ShinoharaTa/keyboards/Shiro/pcb/Shiro/design/siro_mask.png

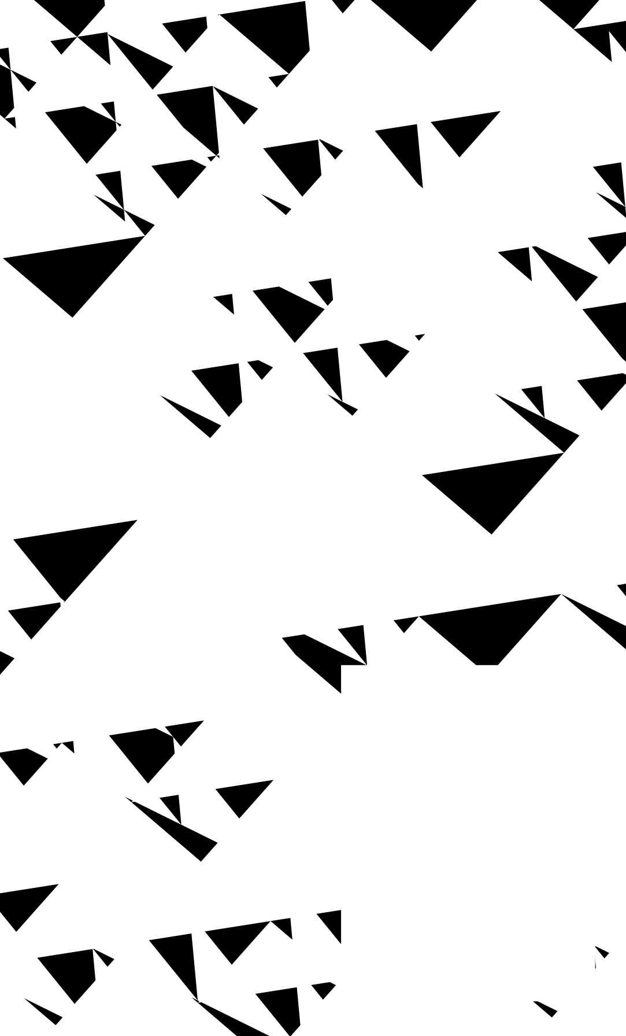
Shiro/pcb/Shiro/design/siro_mask.png
