ShinoharaTa/keyboards/Shiro/pcb/Shiro/design/siro_silk.png

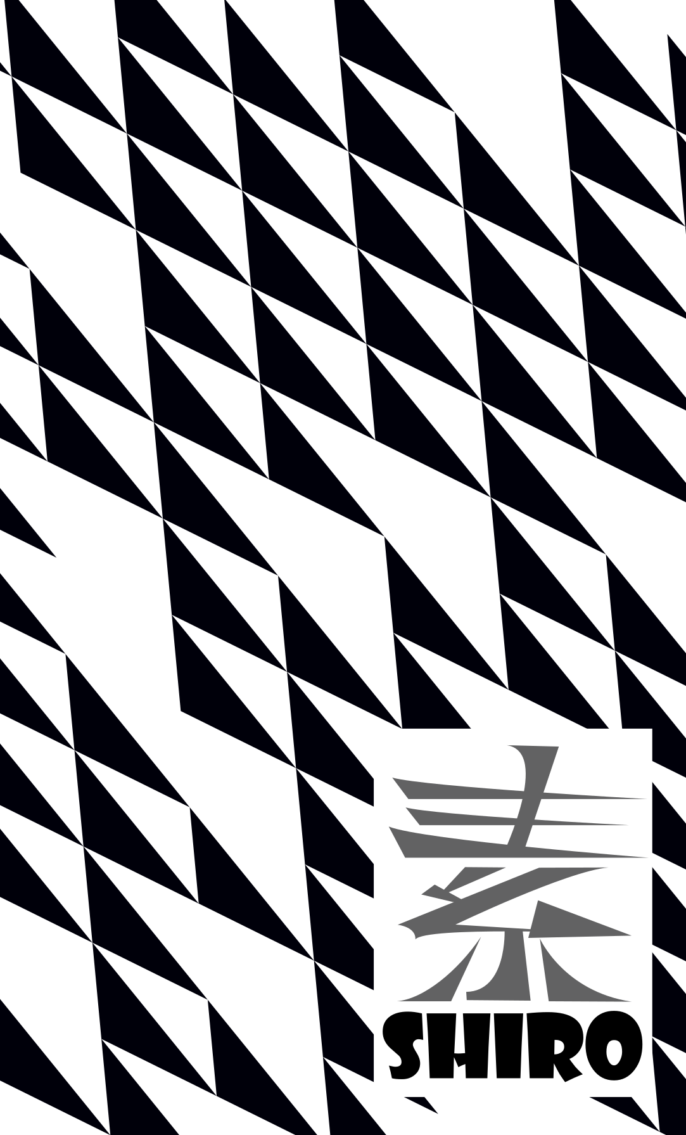
Shiro/pcb/Shiro/design/siro_silk.png
