ShinoharaTa/keyboards/RURA66/manual/images/IMG_0211.jpg

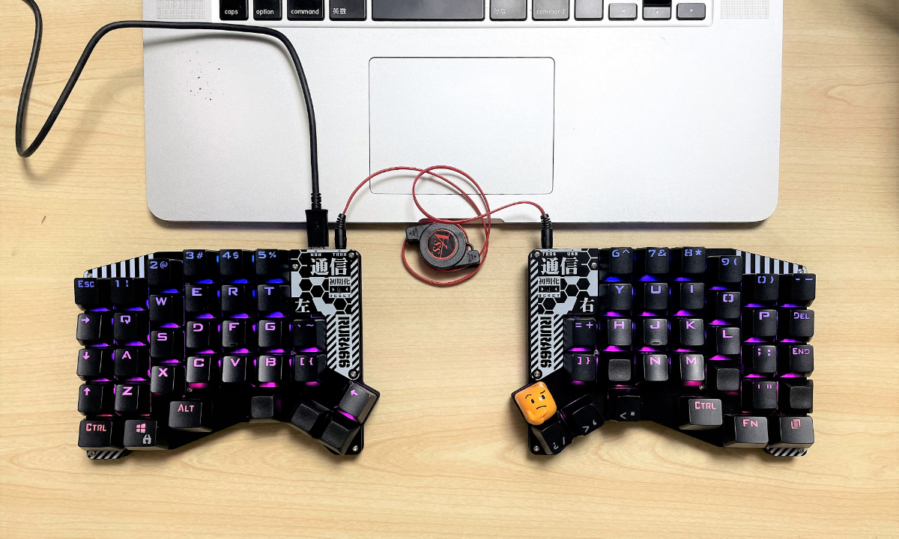
RURA66/manual/images/IMG_0211.jpg
