ShinoharaTa/keyboards/RURA66/manual/images/IMG_0212.jpg

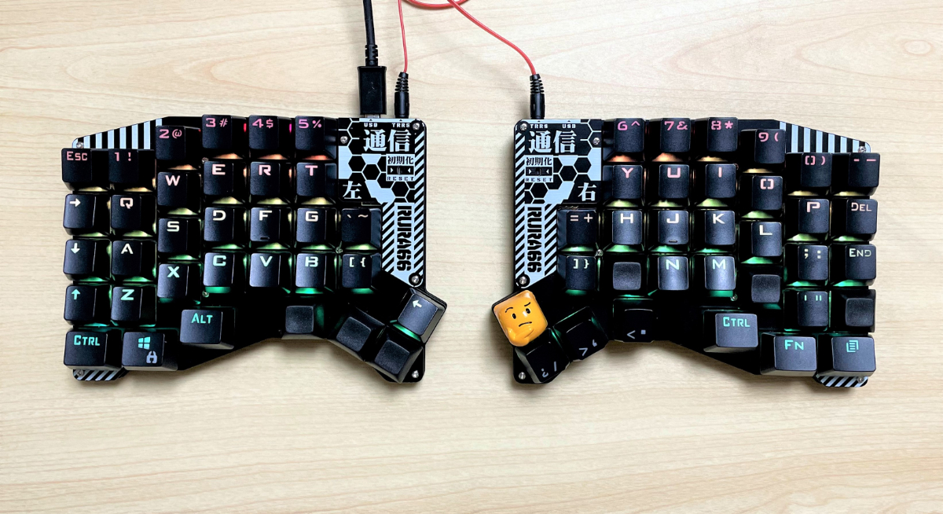
RURA66/manual/images/IMG_0212.jpg
