ShinoharaTa/keyboards/RURA66/manual/images/IMG_0217.jpg

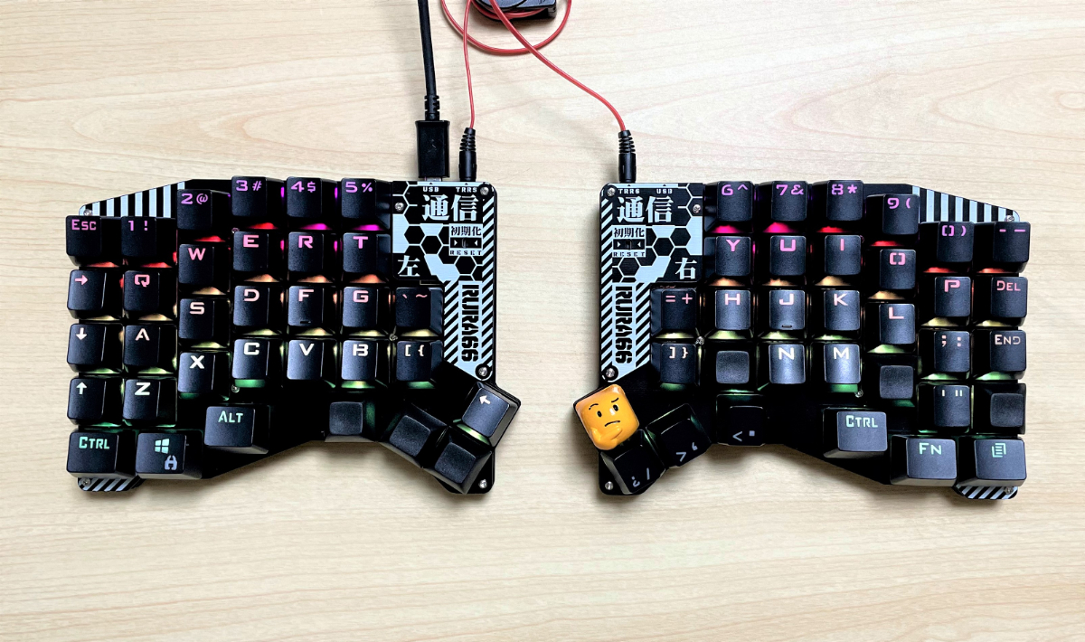
RURA66/manual/images/IMG_0217.jpg
