ShinoharaTa/keyboards/RURA66/manual/images/IMG_0218.jpg

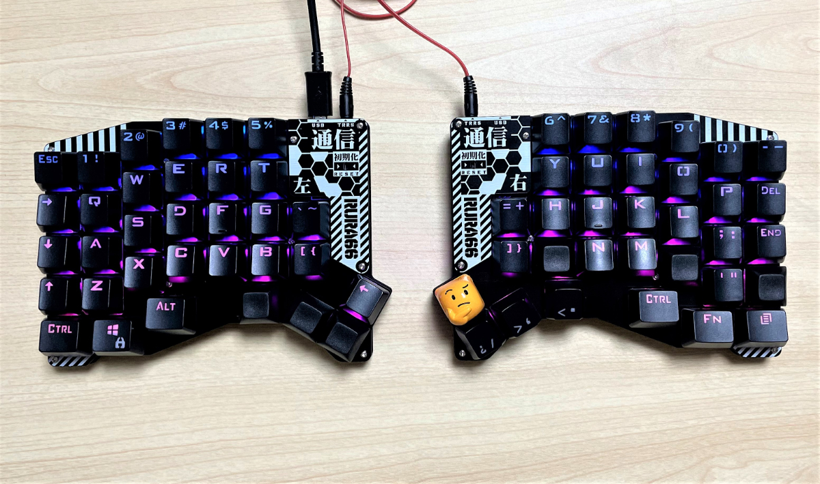
RURA66/manual/images/IMG_0218.jpg
