ShinoharaTa/keyboards/RURA66/manual/images/IMG_0220.jpg

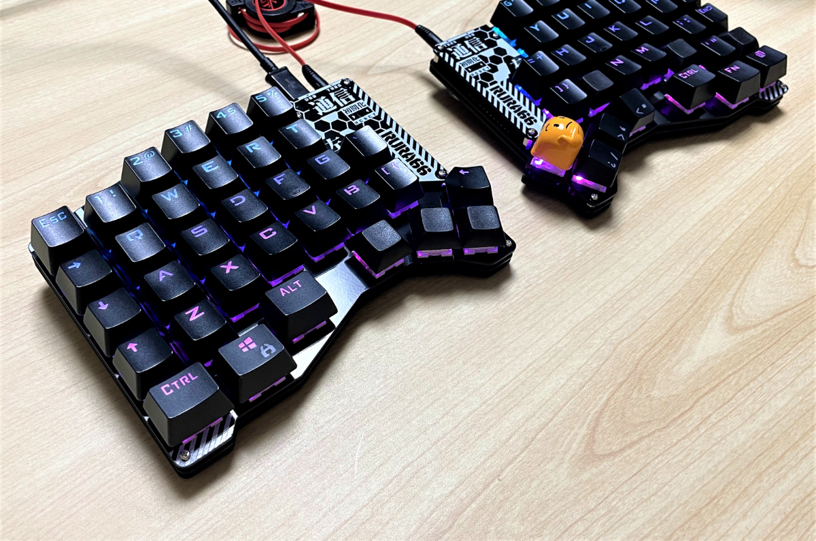
RURA66/manual/images/IMG_0220.jpg
