ShinoharaTa/keyboards/RURA66/manual/images/IMG_0231.jpg

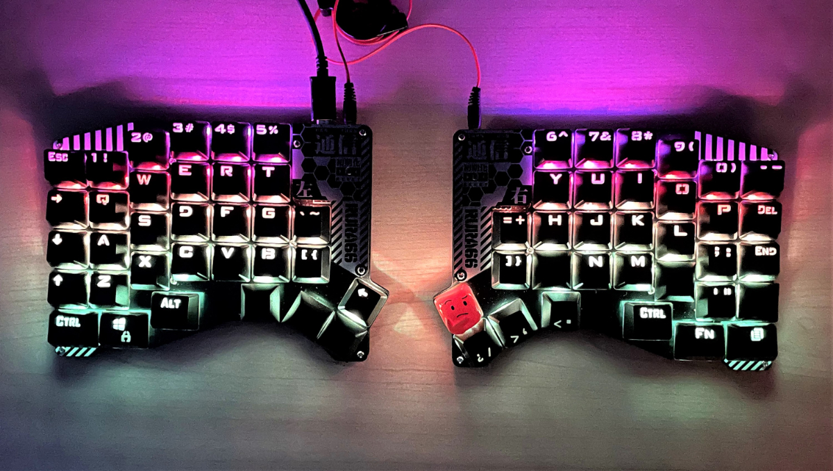
RURA66/manual/images/IMG_0231.jpg
