ShinoharaTa/keyboards/RURA66/manual/images/IMG_0232.jpg

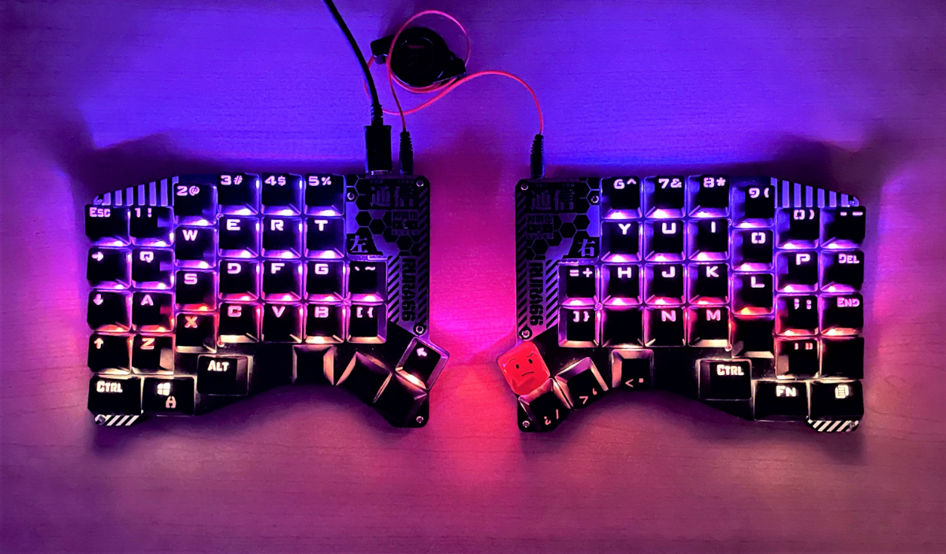
RURA66/manual/images/IMG_0232.jpg
