ShinoharaTa/keyboards/RURA66/manual/images/IMG_0242.jpg

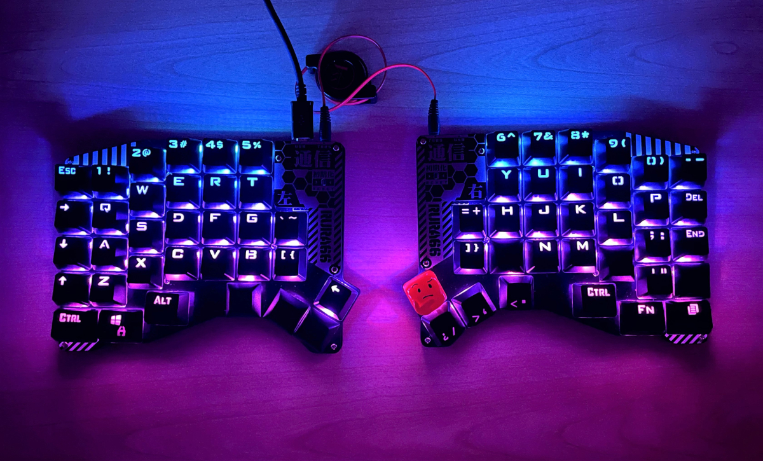
RURA66/manual/images/IMG_0242.jpg
