ShinoharaTa/keyboards/RURA66/manual/images/IMG_0276.jpg

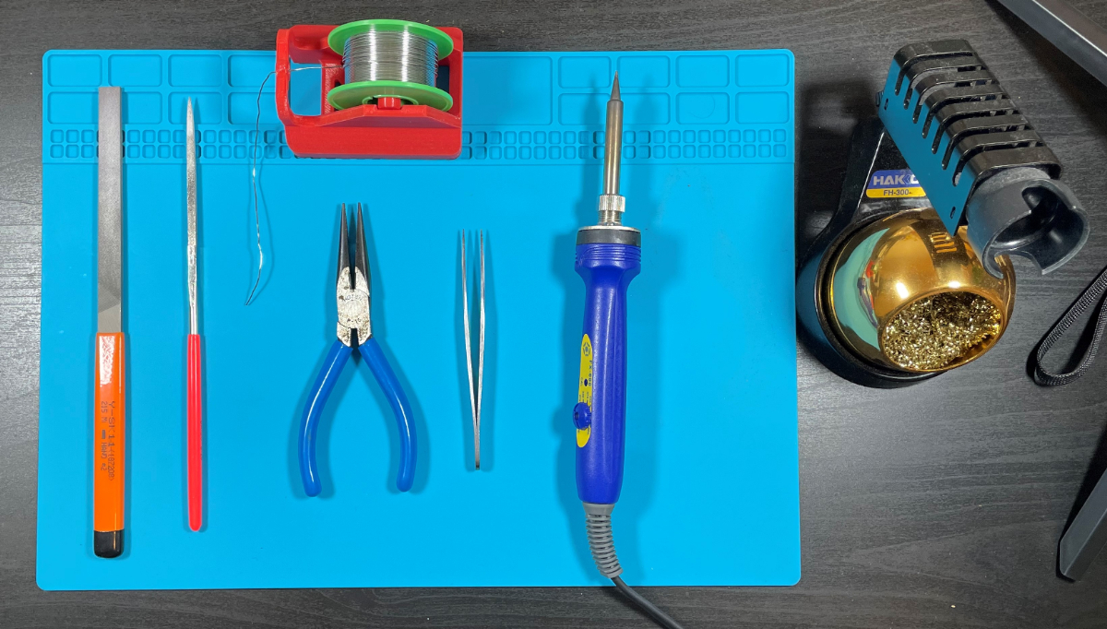
RURA66/manual/images/IMG_0276.jpg
