ShinoharaTa/keyboards/RURA66/manual/images/IMG_0283.jpg

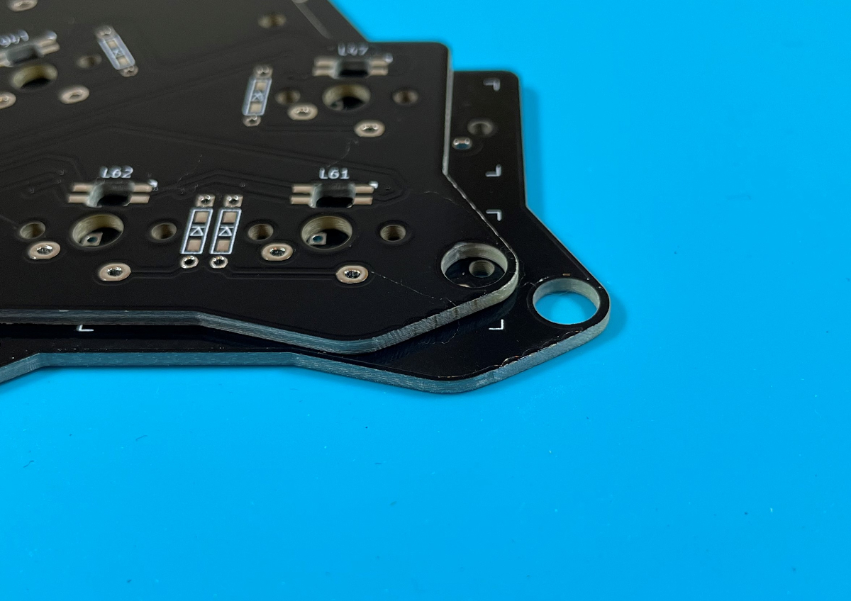
RURA66/manual/images/IMG_0283.jpg
