ShinoharaTa/keyboards/RURA66/manual/images/IMG_0285.jpg

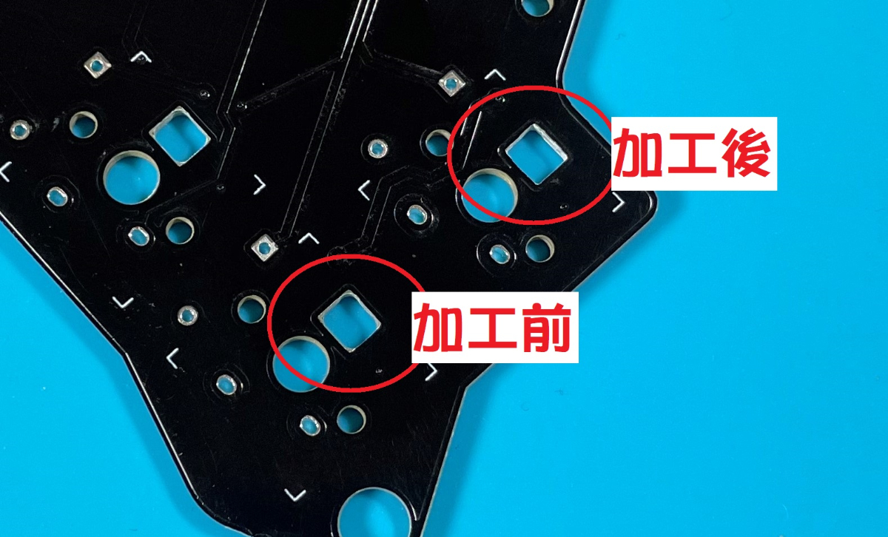
RURA66/manual/images/IMG_0285.jpg
