ShinoharaTa/keyboards/RURA66/manual/images/IMG_0292.jpg

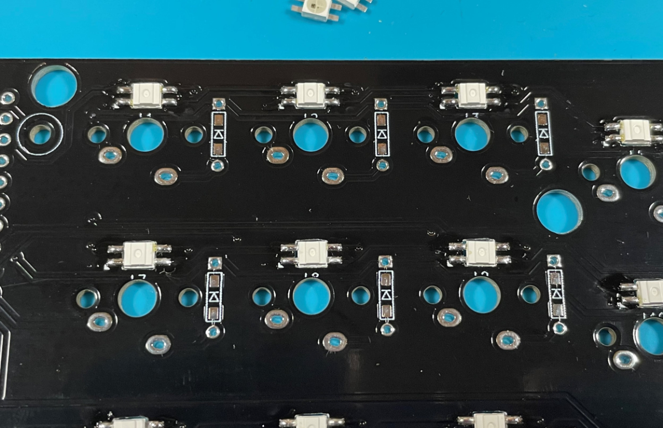
RURA66/manual/images/IMG_0292.jpg
