ShinoharaTa/keyboards/RURA66/manual/images/IMG_0301.jpg

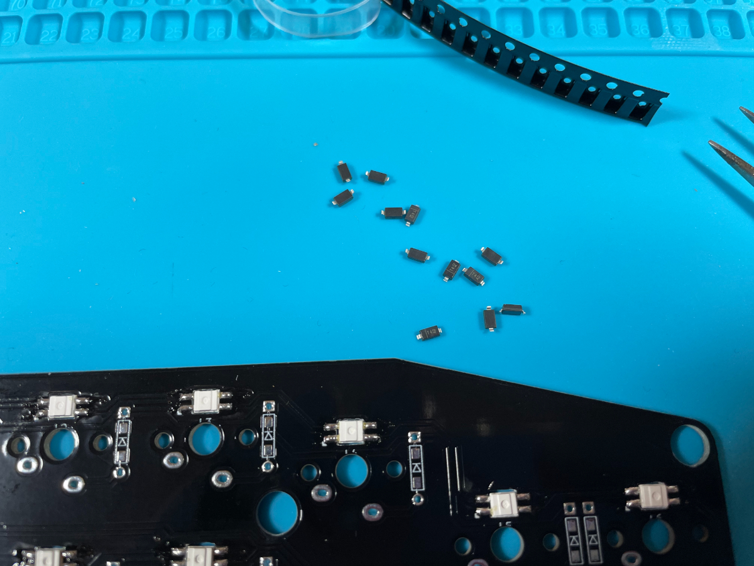
RURA66/manual/images/IMG_0301.jpg
