ShinoharaTa/keyboards/RURA66/manual/images/IMG_0330.jpg

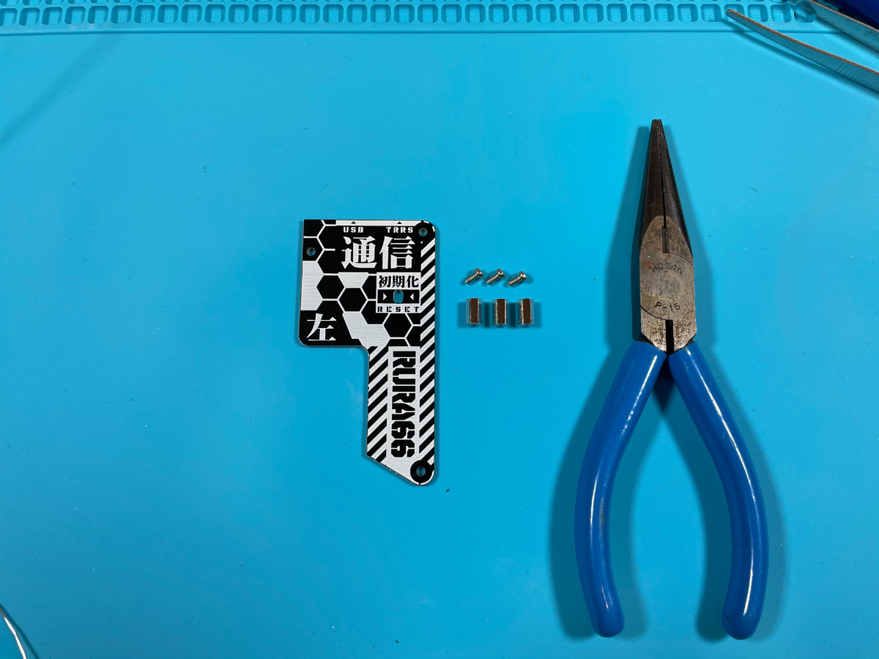
RURA66/manual/images/IMG_0330.jpg
