ShinoharaTa/keyboards/RURA66/manual/images/IMG_0333.jpg

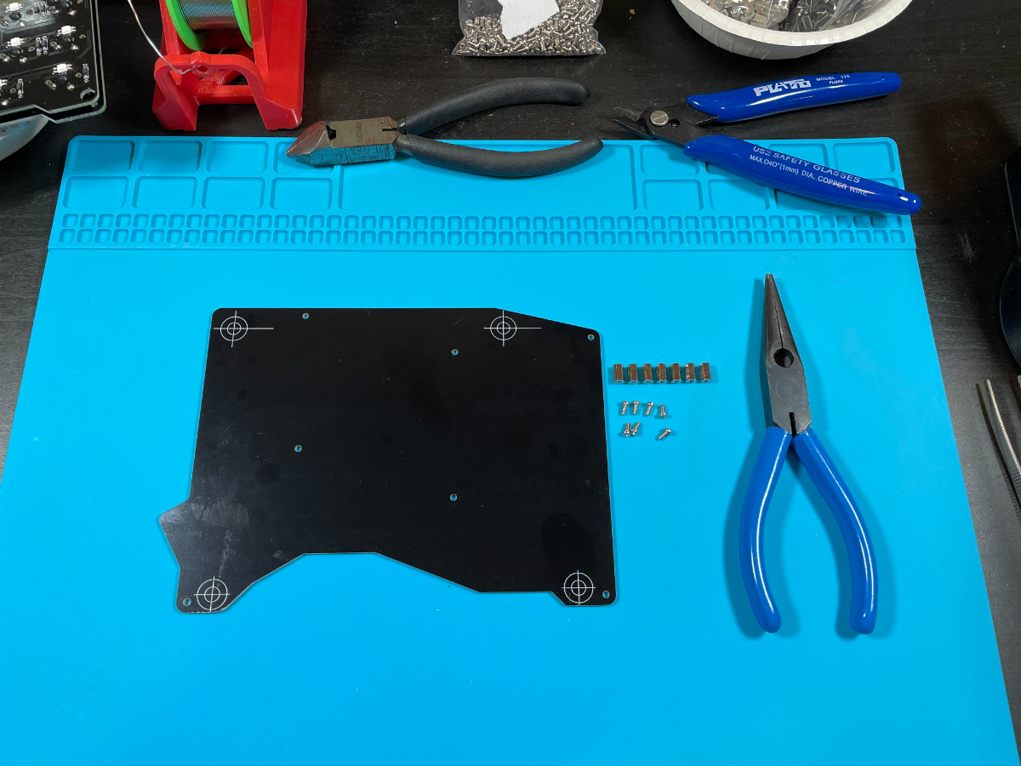
RURA66/manual/images/IMG_0333.jpg
