ShinoharaTa/keyboards/BlackMasK60/firmware/blackmask60/rev1/rev1.c

#include "blackmask60.h"


#ifdef SSD1306OLED
void led_set_kb(uint8_t usb_led) {
    // put your keyboard LED indicator (ex: Caps Lock LED) toggling code here
    //led_set_user(usb_led);
}
#endif

void matrix_init_kb(void) {

	matrix_init_user();
};
