ShinoharaTa/keyboards/BlackMasK60/firmware/blackmask60/rev1/serial_config_simpleapi.h

#ifndef SERIAL_CONFIG_SIMPLEAPI_H
#define SERIAL_CONFIG_SIMPLEAPI_H

#undef SERIAL_USE_MULTI_TRANSACTION
#define SERIAL_SLAVE_BUFFER_LENGTH MATRIX_ROWS/2
#define SERIAL_MASTER_BUFFER_LENGTH MATRIX_ROWS/2

#endif // SERIAL_CONFIG_SIMPLEAPI_H
